Jean-PaulSchappner/parametrischer-Lampenschirm-/makerworld/bilder/03_strickmuster.png

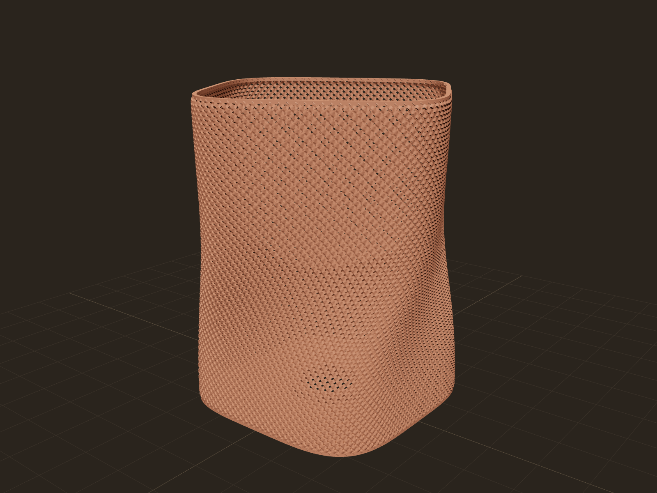
makerworld/bilder/03_strickmuster.png
